strtfnst/uConsole-Parts/STL/Case/Insert.stl

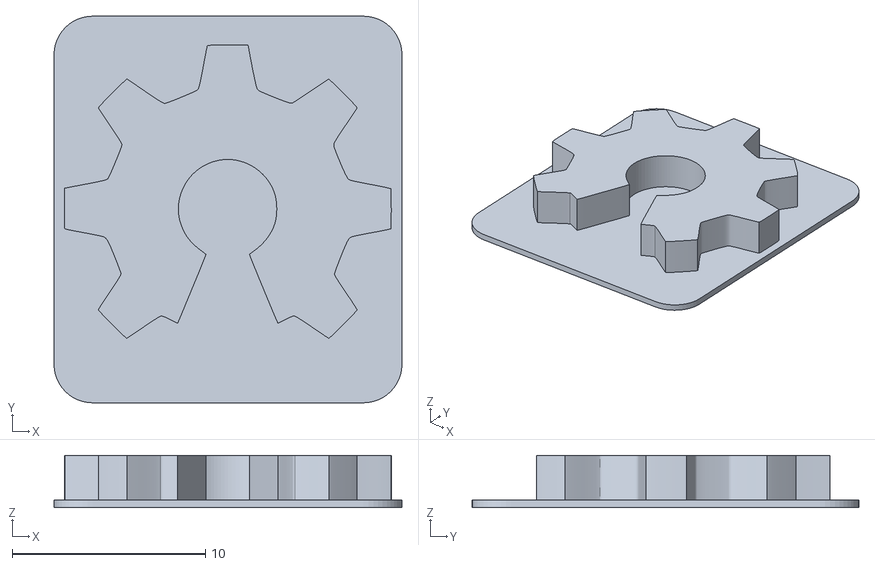
[picture p18: CAD file, 2025-06-01]
STL/Case/Insert.stl
18.0 x 20.0 x 2.70
