strtfnst/uConsole-Parts/STL/HG_Board_cover/pwr_button.stl

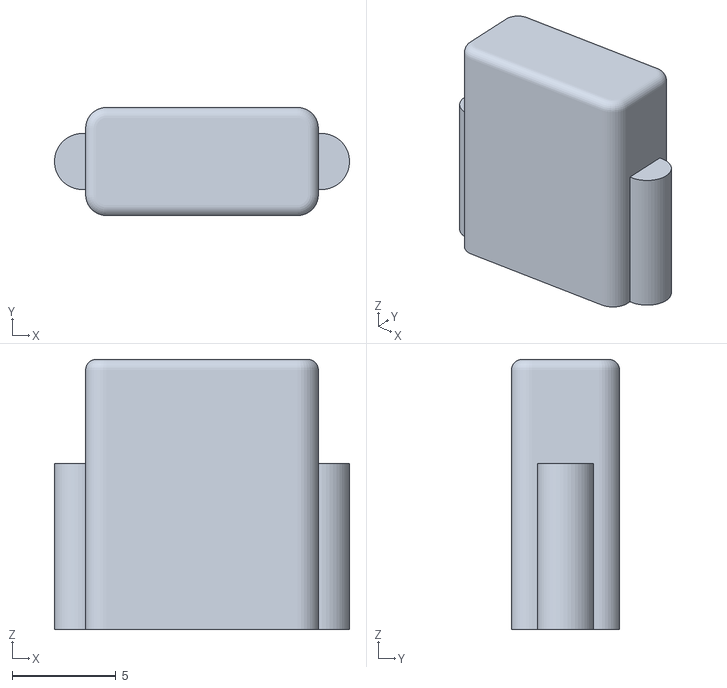
[picture p19: CAD file, 2025-06-09]
STL/HG_Board_cover/pwr_button.stl
14.2 x 5.20 x 13.0
